MotorDynamicsLab/LDO-Milo-V1.5/STLs/Minimill Main/Spindle Mount/Logo Insert x1.step

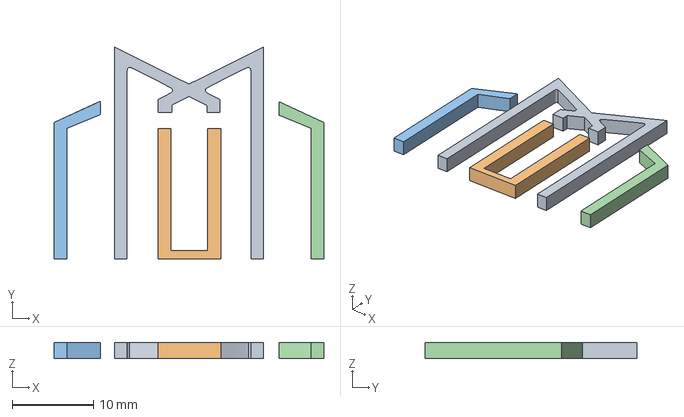
[picture p28: CAD file, 2024-02-10]
STLs/Minimill Main/Spindle Mount/Logo Insert x1.step
33.2 x 26.1 x 2.00 mm
