MotorDynamicsLab/LDO-Milo-V1.5/STLs/Minimill Main/X Axis STLs/X Axis Bearing Block x1_LDO.step

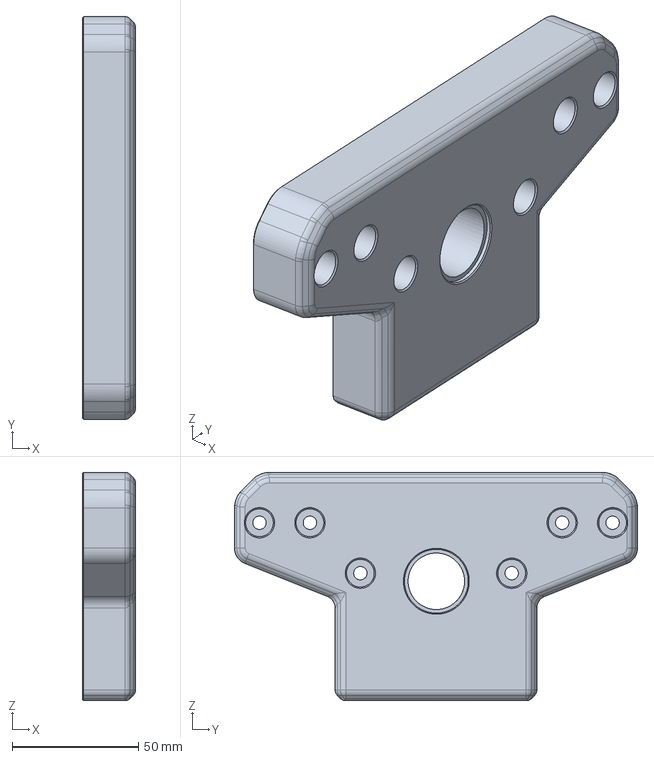
[picture p29: CAD file, 2024-02-22]
STLs/Minimill Main/X Axis STLs/X Axis Bearing Block x1_LDO.step
21.0 x 159.8 x 90.5 mm
