MotorDynamicsLab/LDO-Milo-V1.5/STLs/Minimill Main/Y Axis STLs/Y Axis Bearing Block x1_LDO.step

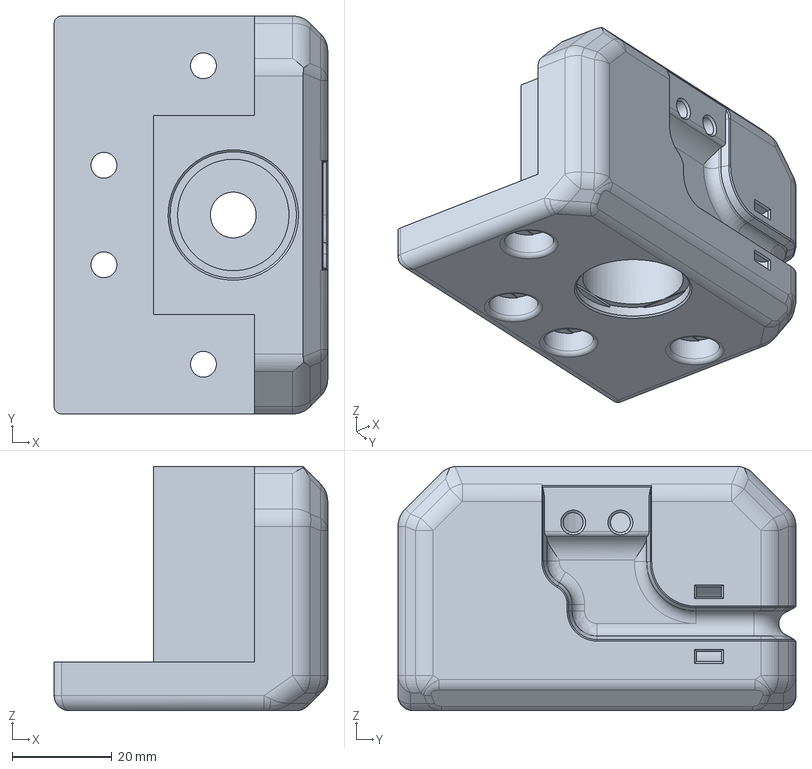
[picture p30: CAD file, 2024-02-22]
STLs/Minimill Main/Y Axis STLs/Y Axis Bearing Block x1_LDO.step
55.0 x 80.0 x 49.1 mm
