MotorDynamicsLab/LDO-Milo-V1.5/STLs/Tools/Rail Alignment Guide.stl

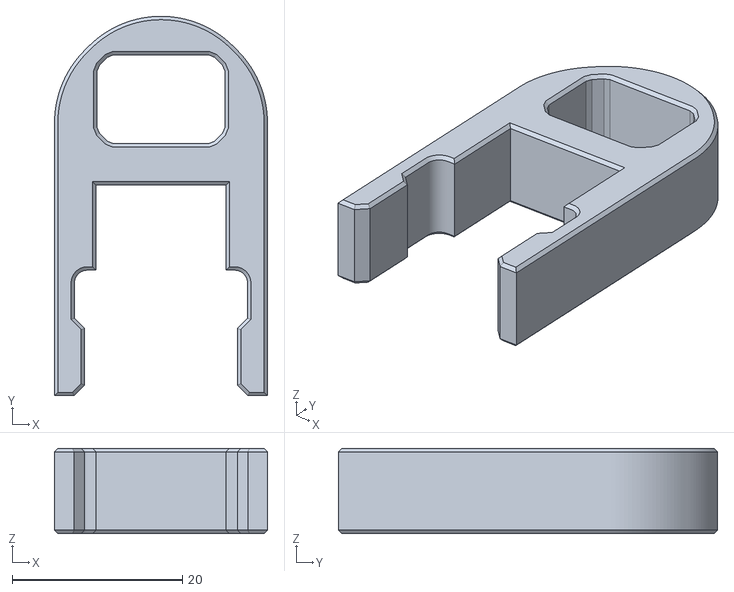
[picture p31: CAD file, 2024-01-26]
STLs/Tools/Rail Alignment Guide.stl
25.0 x 44.5 x 10.0
