MotorDynamicsLab/LDO-Milo-V1.5/STLs/Electronics Table/Rear Skirt B x1.step

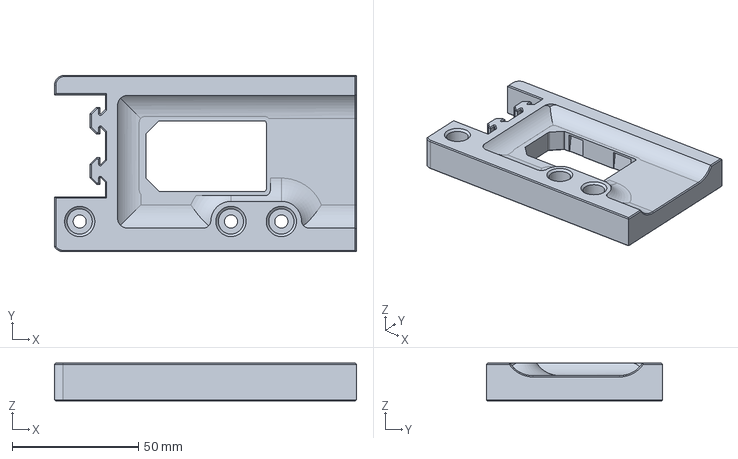
[picture p32: CAD file, 2024-03-12]
STLs/Electronics Table/Rear Skirt B x1.step
119.8 x 70.0 x 15.0 mm
