MotorDynamicsLab/LDO-Milo-V1.5/STLs/Minimill Main/Cable Chain Mounts/[a] Z Top Cable Tie Anchor_LDO.step

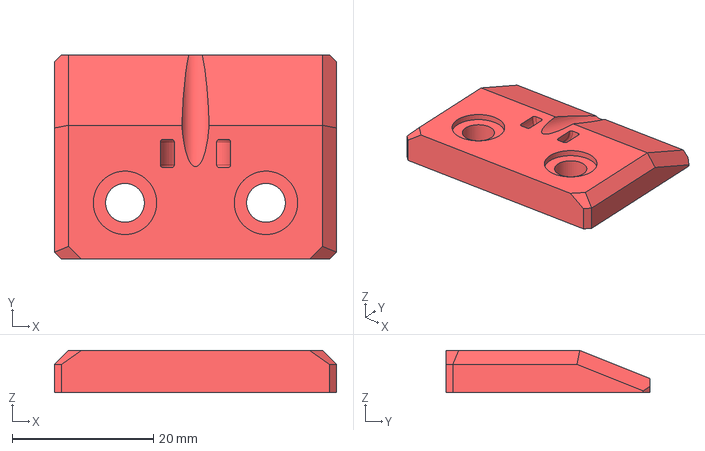
[picture p33: CAD file, 2024-02-10]
STLs/Minimill Main/Cable Chain Mounts/[a] Z Top Cable Tie Anchor_LDO.step
40.0 x 29.0 x 6.00 mm
