MotorDynamicsLab/LDO-Milo-V1.5/STLs/Minimill Main/Hand Wheels/Handwheel Handle x2.stl

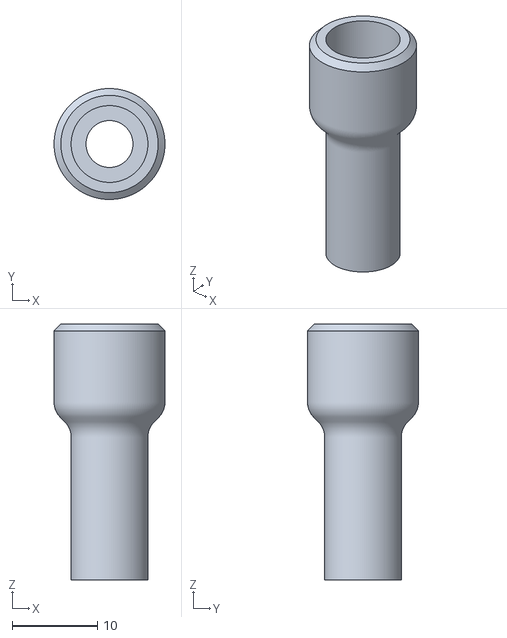
[picture p34: CAD file, 2024-01-26]
STLs/Minimill Main/Hand Wheels/Handwheel Handle x2.stl
13.0 x 13.0 x 30.0
