MotorDynamicsLab/LDO-Milo-V1.5/STLs/Minimill Main/Millenium Maker Coin.stl

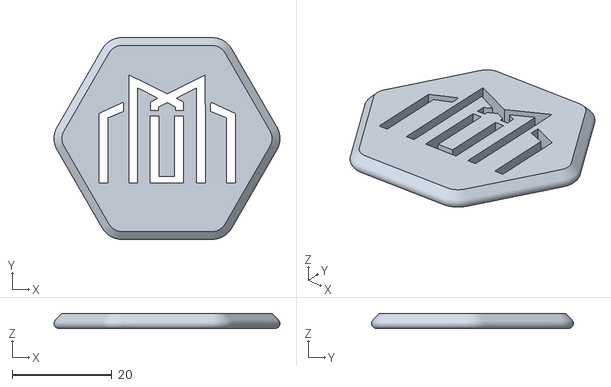
[picture p35: CAD file, 2024-01-26]
STLs/Minimill Main/Millenium Maker Coin.stl
45.3 x 40.5 x 3.00
