MotorDynamicsLab/LDO-Milo-V1.5/STLs/Minimill Main/Spindle Mount/[a][24] Spindle Mount 80mm Part A x1_LDO.step

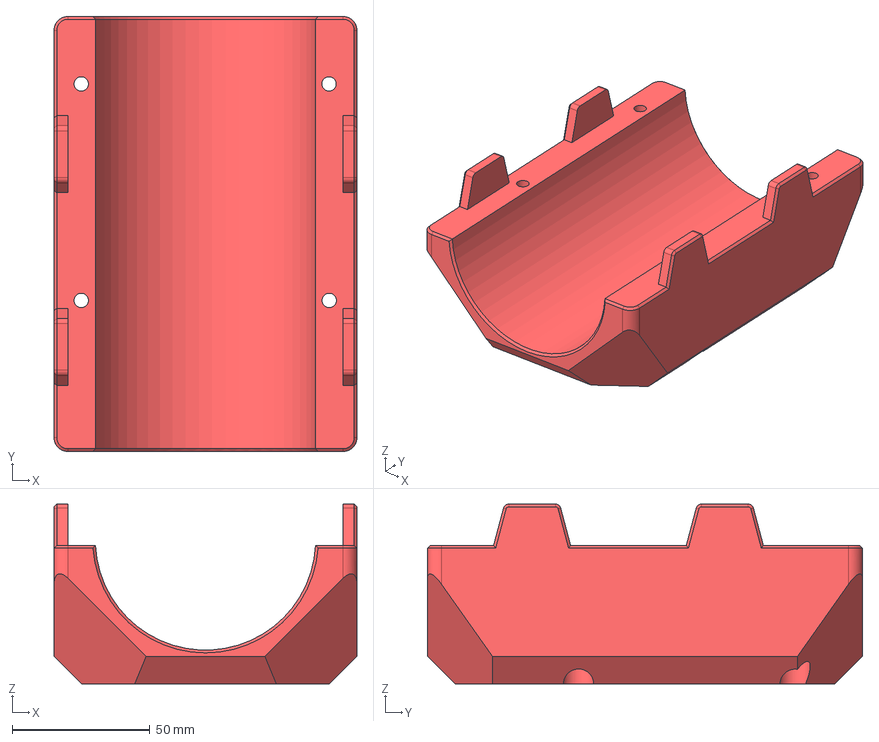
[picture p36: CAD file, 2024-02-10]
STLs/Minimill Main/Spindle Mount/[a][24] Spindle Mount 80mm Part A x1_LDO.step
110.0 x 158.0 x 65.4 mm
