MotorDynamicsLab/LDO-Milo-V1.5/STLs/Minimill Main/X Axis STLs/X Axis Table Support Centre x2_LDO.step

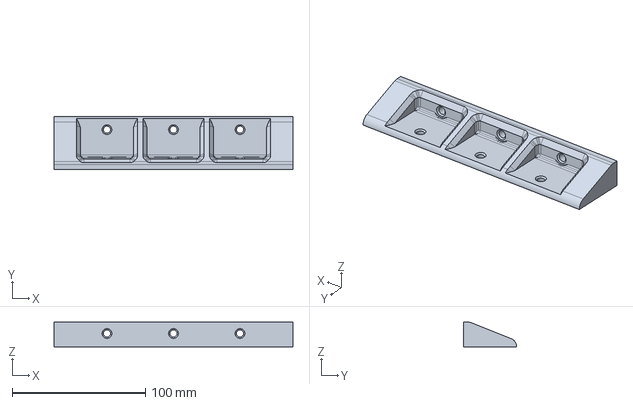
[picture p37: CAD file, 2024-02-10]
STLs/Minimill Main/X Axis STLs/X Axis Table Support Centre x2_LDO.step
179.6 x 40.0 x 18.5 mm
