MotorDynamicsLab/LDO-Milo-V1.5/STLs/Minimill Main/Y Axis STLs/Y Axis Motor Mount x1_LDO.step

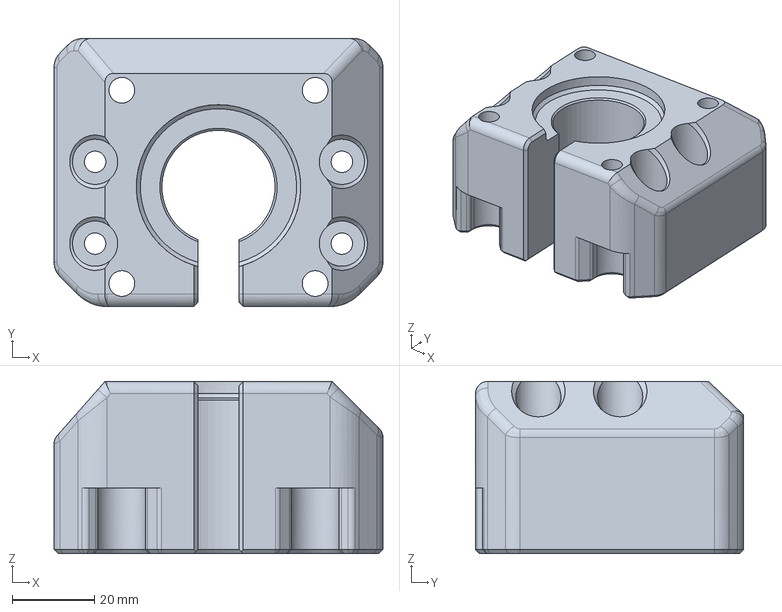
[picture p38: CAD file, 2024-02-10]
STLs/Minimill Main/Y Axis STLs/Y Axis Motor Mount x1_LDO.step
80.0 x 65.2 x 41.9 mm
