MotorDynamicsLab/LDO-Milo-V1.5/STLs/Minimill Main/Z Axis STLs/Z Motor Mount x1_LDO.step

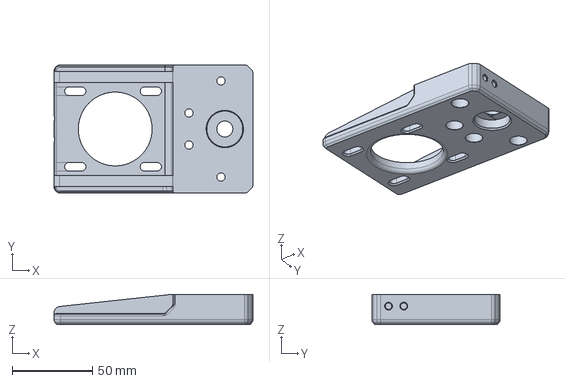
[picture p39: CAD file, 2024-02-10]
STLs/Minimill Main/Z Axis STLs/Z Motor Mount x1_LDO.step
124.2 x 80.0 x 19.0 mm
