MotorDynamicsLab/LDO-Milo-V1.5/STLs/Electronics Table/PSU Mounting Brackets  x1_LDO.step

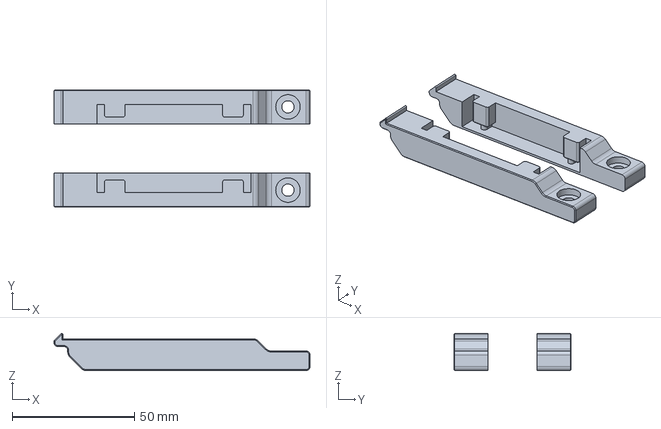
[picture p40: CAD file, 2024-02-21]
STLs/Electronics Table/PSU Mounting Brackets x1_LDO.step
104.6 x 48.0 x 15.2 mm
Left
Right
