MotorDynamicsLab/LDO-Milo-V1.5/STLs/Minimill Main/Cable Chain Mounts/[a] Z Drag Chain Mount B x1_LDO.step

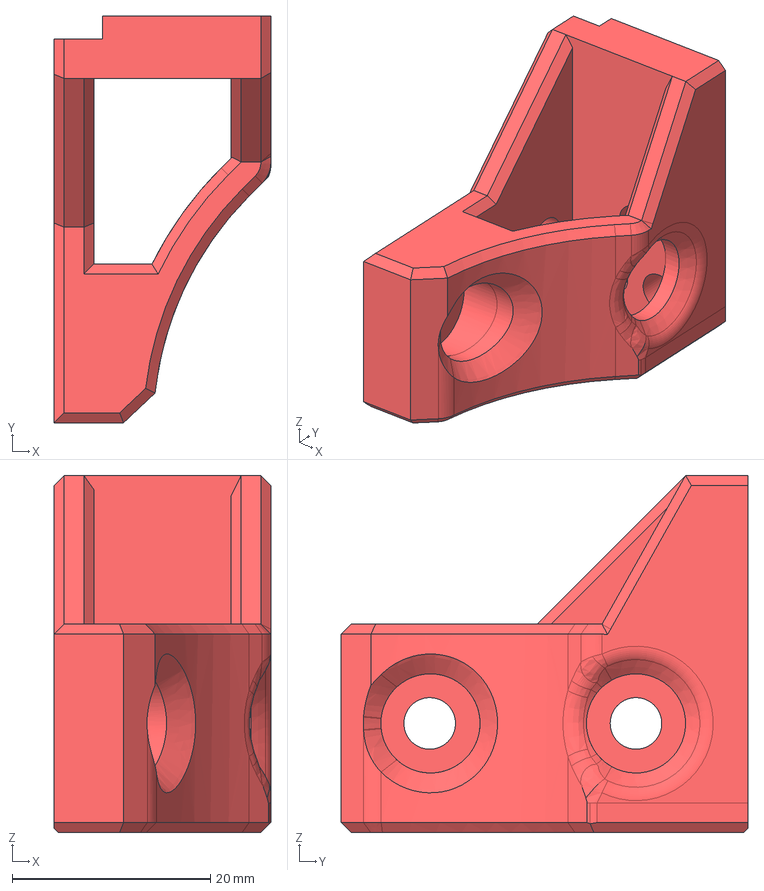
[picture p41: CAD file, 2024-02-10]
STLs/Minimill Main/Cable Chain Mounts/[a] Z Drag Chain Mount B x1_LDO.step
21.9 x 41.0 x 36.0 mm
