MotorDynamicsLab/LDO-Milo-V1.5/STLs/Minimill Main/X Axis STLs/X Axis Motor Mount x1_LDO.step

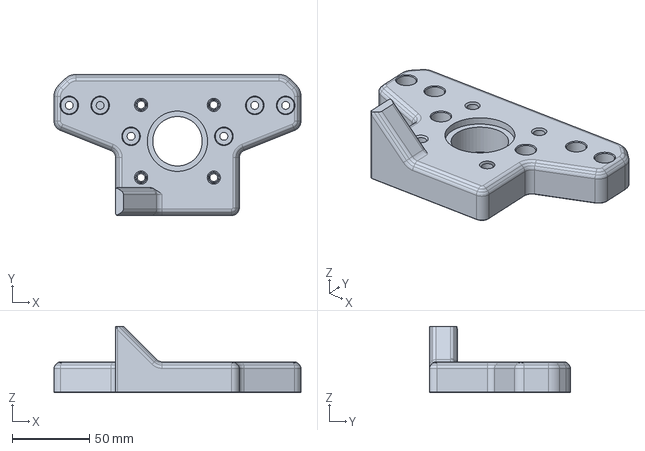
[picture p42: CAD file, 2024-02-10]
STLs/Minimill Main/X Axis STLs/X Axis Motor Mount x1_LDO.step
159.8 x 91.3 x 43.0 mm
