MotorDynamicsLab/LDO-Milo-V1.5/STLs/Electronics Table/Rear Skirt A x1.step

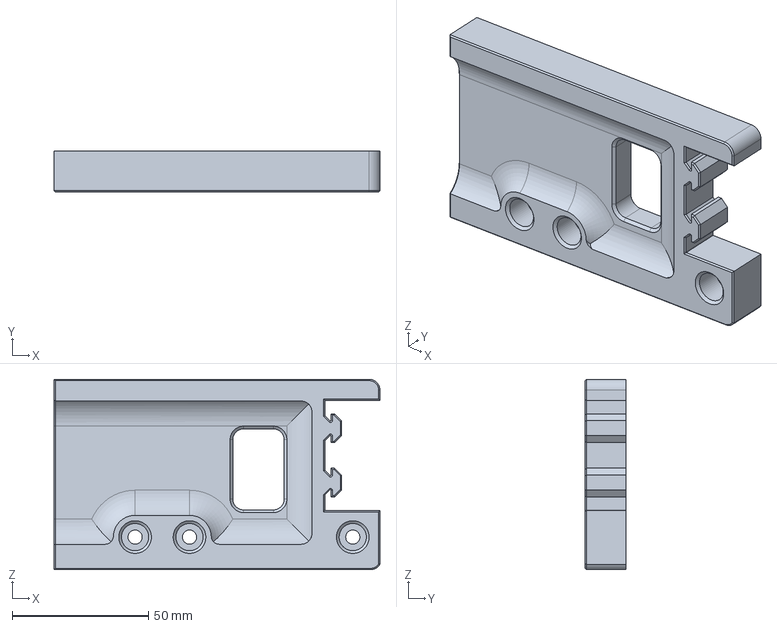
[picture p43: CAD file, 2024-02-12]
STLs/Electronics Table/Rear Skirt A x1.step
119.8 x 15.0 x 70.0 mm
