MotorDynamicsLab/LDO-Milo-V1.5/STLs/Minimill Main/Cable Chain Mounts/[a] Y Drag Chain Mount x1.step

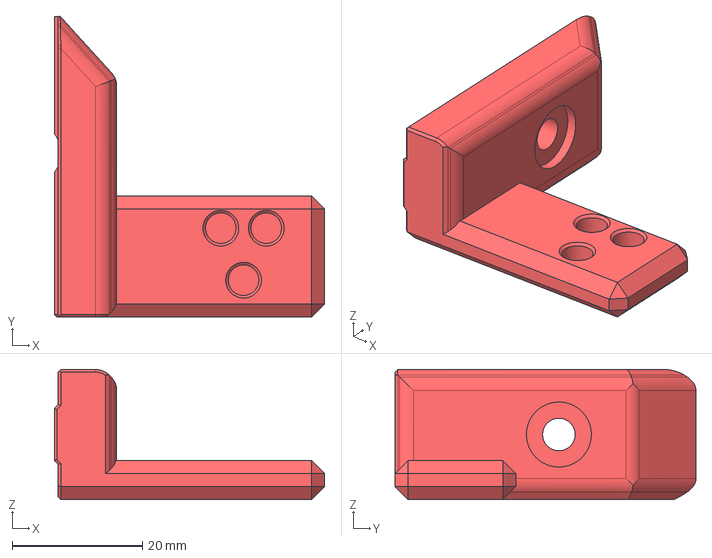
[picture p44: CAD file, 2024-02-10]
STLs/Minimill Main/Cable Chain Mounts/[a] Y Drag Chain Mount x1.step
41.6 x 46.3 x 20.0 mm
