MotorDynamicsLab/LDO-Milo-V1.5/STLs/Minimill Main/X Axis STLs/X Axis Table Support Ends x4_LDO.step

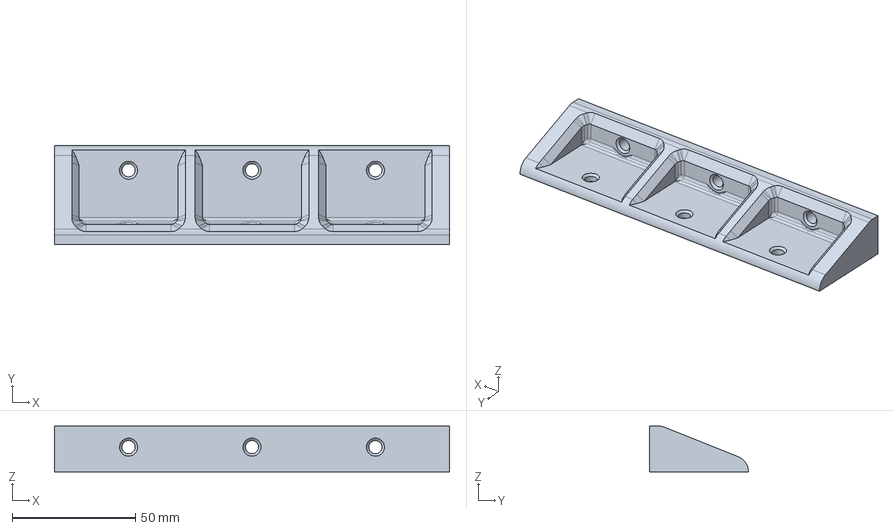
[picture p45: CAD file, 2024-02-10]
STLs/Minimill Main/X Axis STLs/X Axis Table Support Ends x4_LDO.step
160.0 x 40.0 x 18.5 mm
