MotorDynamicsLab/LDO-Milo-V1.5/STLs/Minimill Main/Cable Chain Mounts/[a] Z Drag Chain Mount A x1_LDO.step

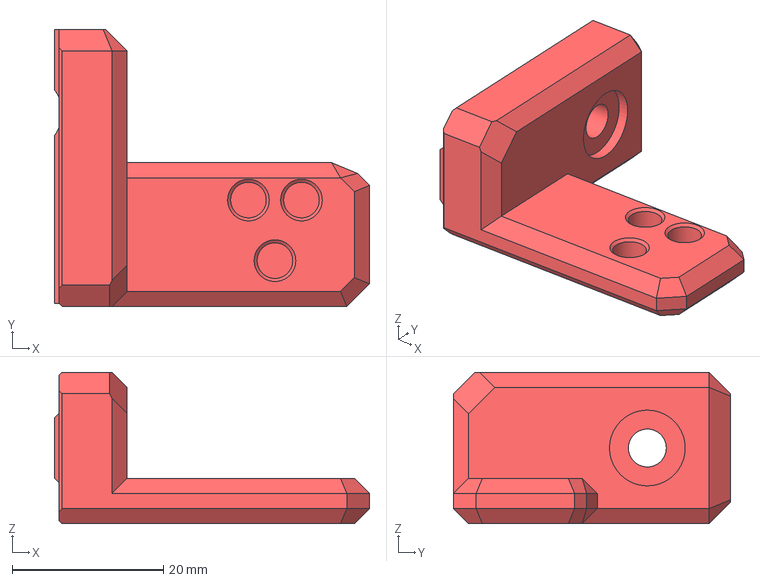
[picture p46: CAD file, 2024-02-10]
STLs/Minimill Main/Cable Chain Mounts/[a] Z Drag Chain Mount A x1_LDO.step
41.6 x 36.6 x 20.0 mm
