MotorDynamicsLab/LDO-Milo-V1.5/STLs/Electronics Table/Skirt Front A Solid x1.step

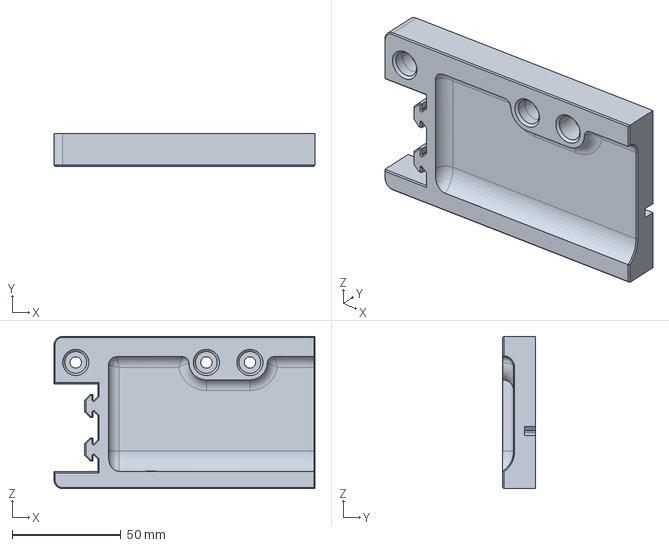
[picture p47: CAD file, 2024-02-12]
STLs/Electronics Table/Skirt Front A Solid x1.step
119.9 x 15.0 x 70.0 mm
