MotorDynamicsLab/LDO-Milo-V1.5/STLs/Minimill Main/Cable Chain Mounts/[a] Z Axis Cable Chain Backer x1_LDO.step

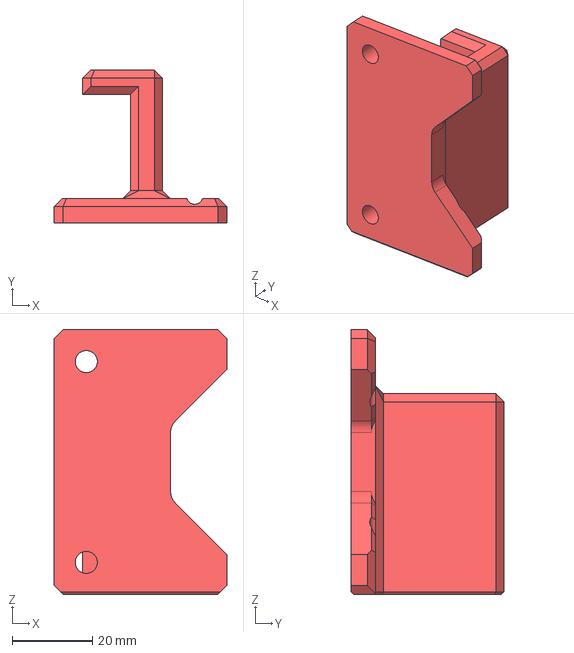
[picture p48: CAD file, 2024-02-10]
STLs/Minimill Main/Cable Chain Mounts/[a] Z Axis Cable Chain Backer x1_LDO.step
43.0 x 38.0 x 66.0 mm
