MotorDynamicsLab/LDO-Milo-V1.5/STLs/Minimill Main/Cable Chain Mounts/[a] Z Cable Redirect Hook x1.stl

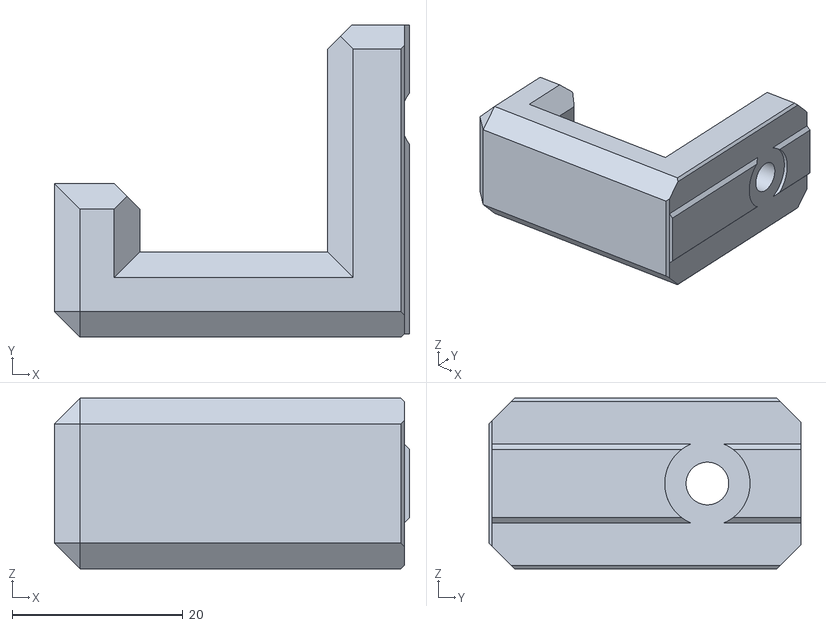
[picture p49: CAD file, 2024-01-26]
STLs/Minimill Main/Cable Chain Mounts/[a] Z Cable Redirect Hook x1.stl
41.6 x 36.6 x 20.0
