MotorDynamicsLab/LDO-Milo-V1.5/STLs/Electronics Table/IO Expander DIN Mount  x1_LDO.step

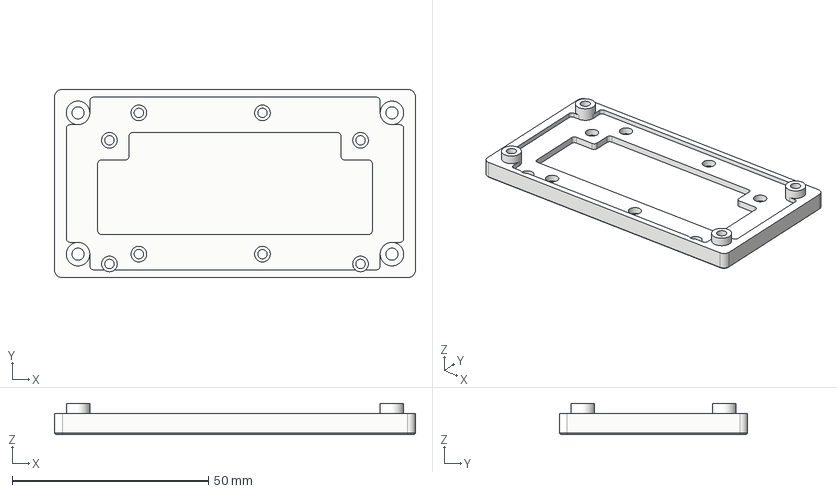
[picture p50: CAD file, 2024-02-10]
STLs/Electronics Table/IO Expander DIN Mount x1_LDO.step
92.0 x 48.0 x 8.00 mm
