MotorDynamicsLab/LDO-Milo-V1.5/STLs/Electronics Table/IO Expander Mount  x1_LDO.step

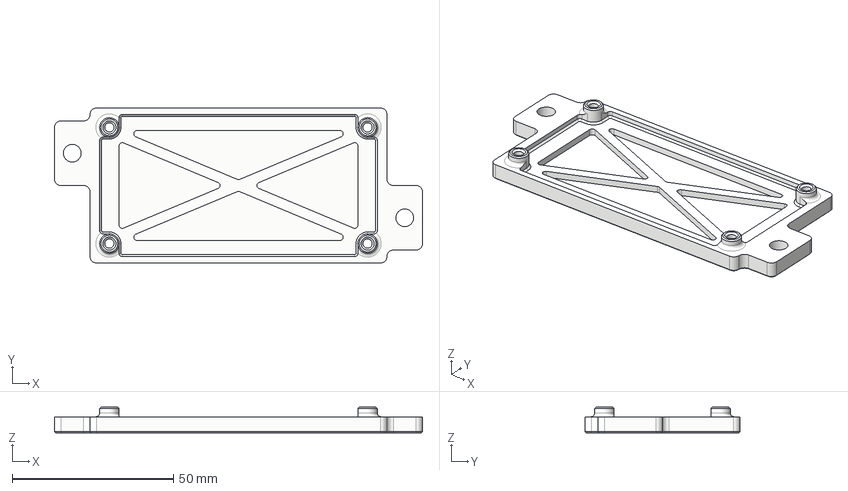
[picture p51: CAD file, 2024-02-10]
STLs/Electronics Table/IO Expander Mount x1_LDO.step
114.0 x 48.0 x 8.00 mm
