MotorDynamicsLab/LDO-Milo-V1.5/STLs/Electronics Table/Cable Channel Cover x1.stl

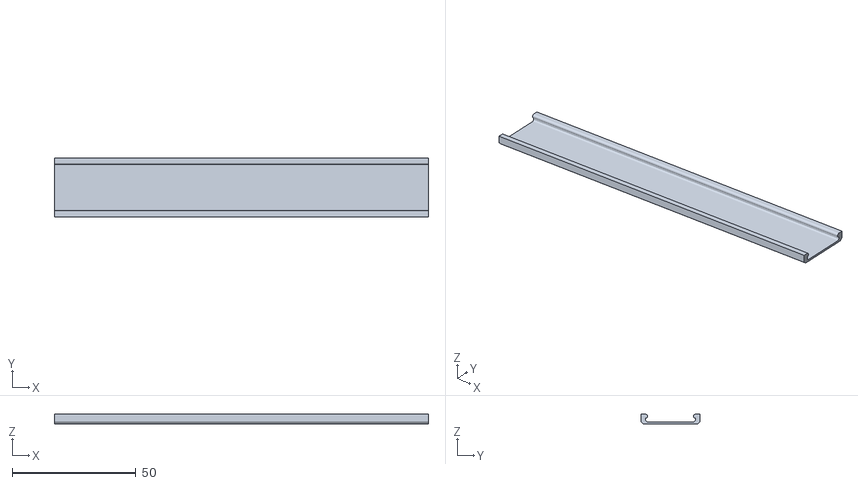
[picture p52: CAD file, 2024-01-26]
STLs/Electronics Table/Cable Channel Cover x1.stl
151.0 x 24.0 x 3.89
