MotorDynamicsLab/LDO-Milo-V1.5/STLs/Electronics Table/TPU Feet x4.stl

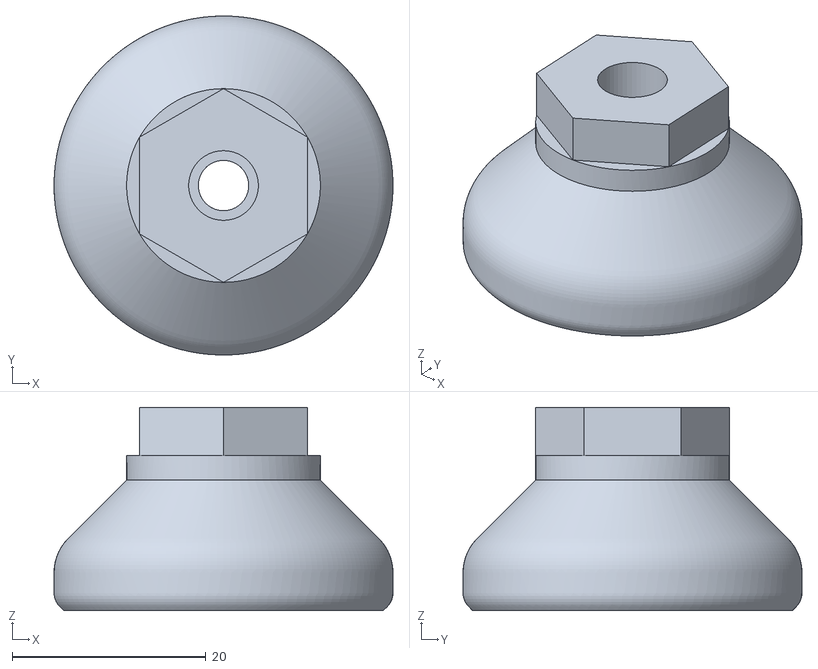
[picture p53: CAD file, 2024-01-26]
STLs/Electronics Table/TPU Feet x4.stl
35.0 x 35.0 x 21.0
